Dutchy94/3D-Laser-Scanner/Python/output/charuco/charuco_A4.png

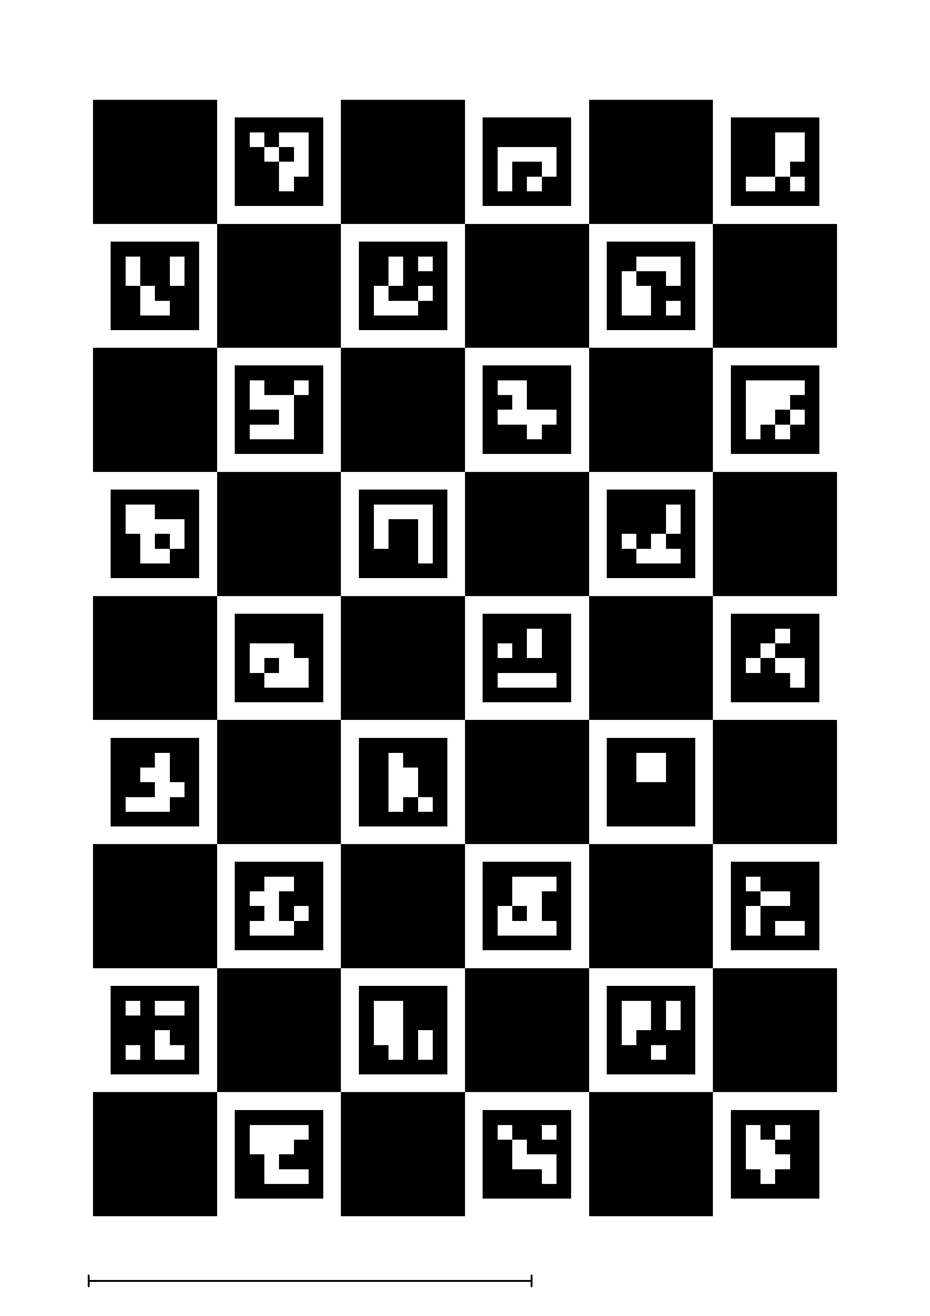
Python/output/charuco/charuco_A4.png
